Adithya-Vishnu/LRC-2025-LAMe-Finalist-Submission/CAD/Component.step

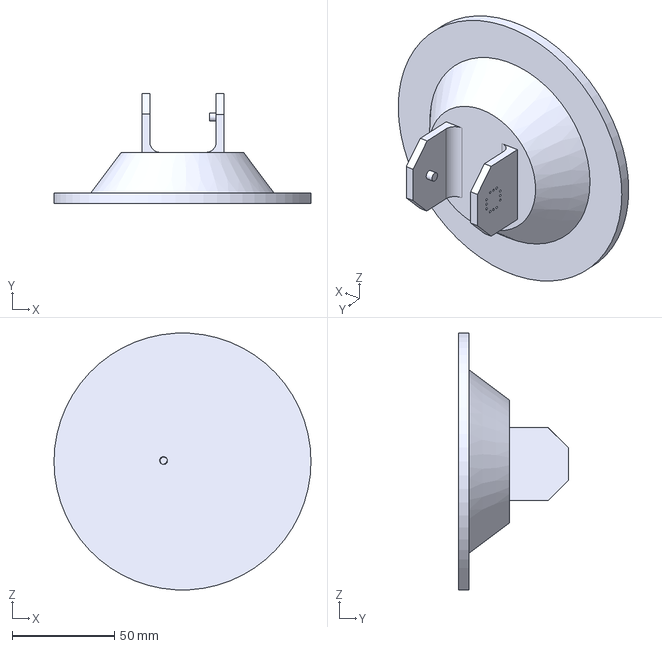
[picture p26: CAD file, 2026-06-22]
CAD/Component.step
125.8 x 53.8 x 125.6 mm
